SHIMA-R7/Famicom-Expand-USB-Adapter/hardware/schematic/famicom-expand-usb-adapter.kicad_sch

## KiCad design hardware/schematic/famicom-expand-usb-adapter.kicad_sch (2026-08-02)

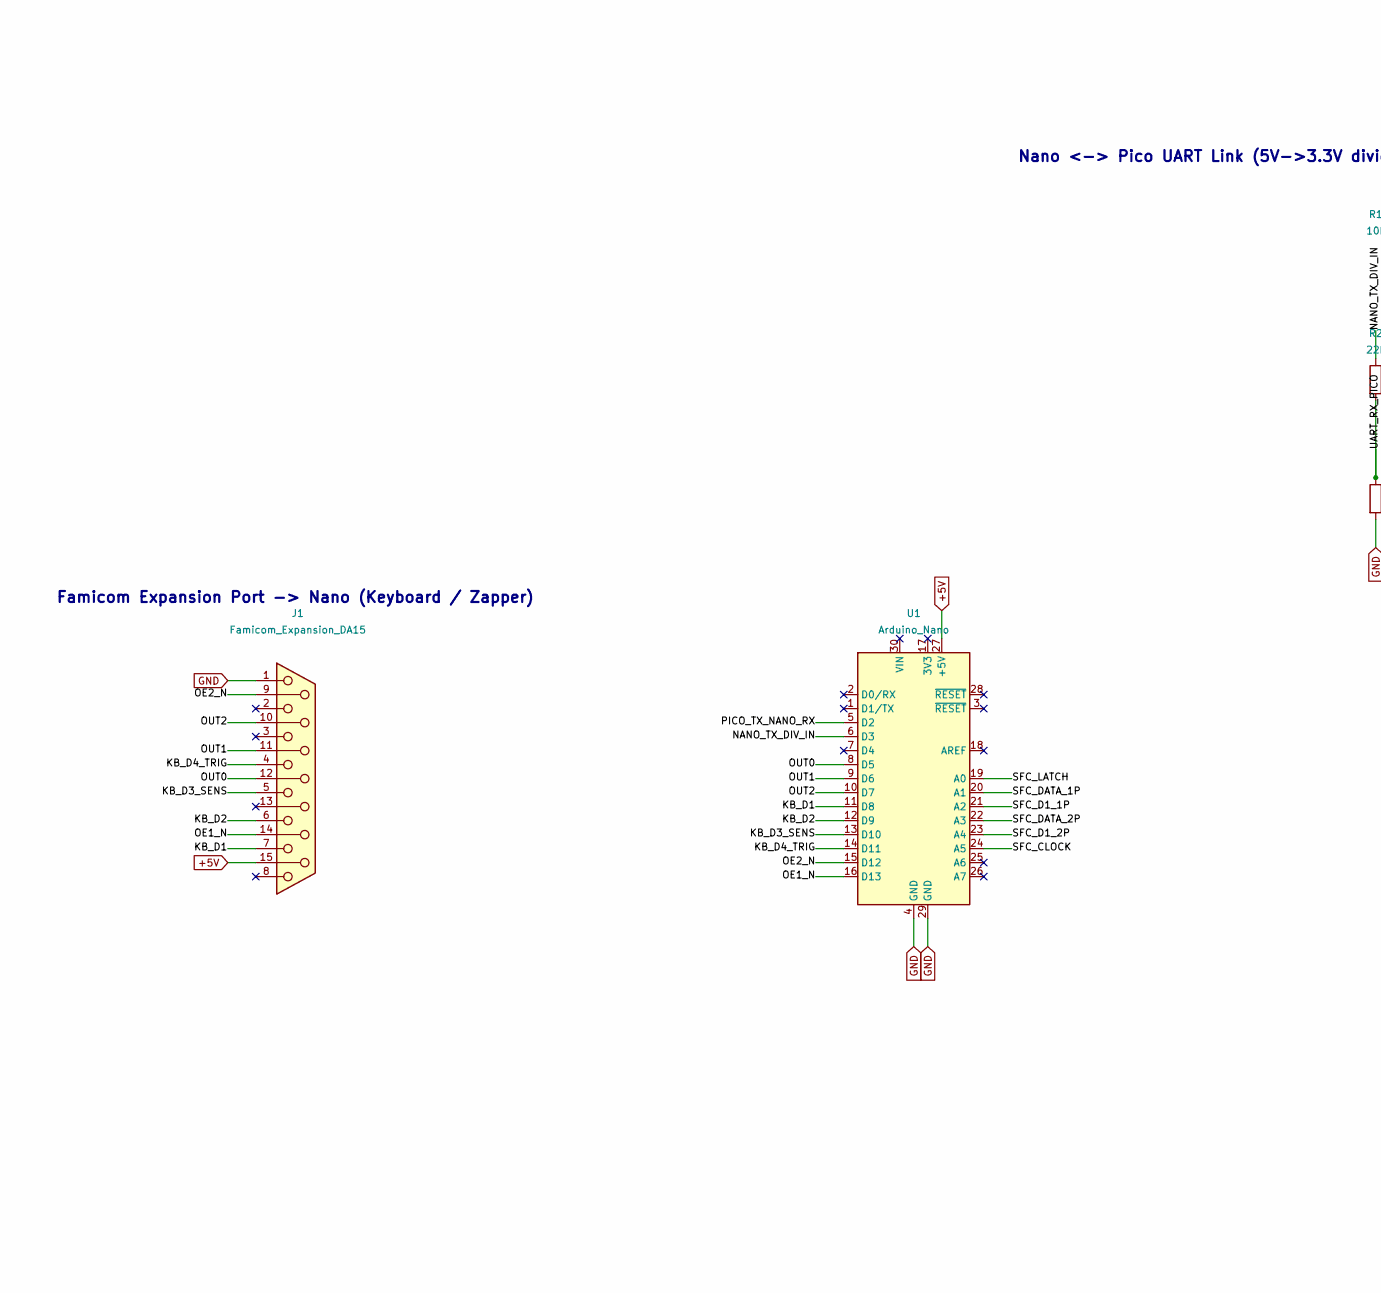
[picture p5: schematic famicom-expand-usb-adapter.kicad_sch, part in row 1, column 1]

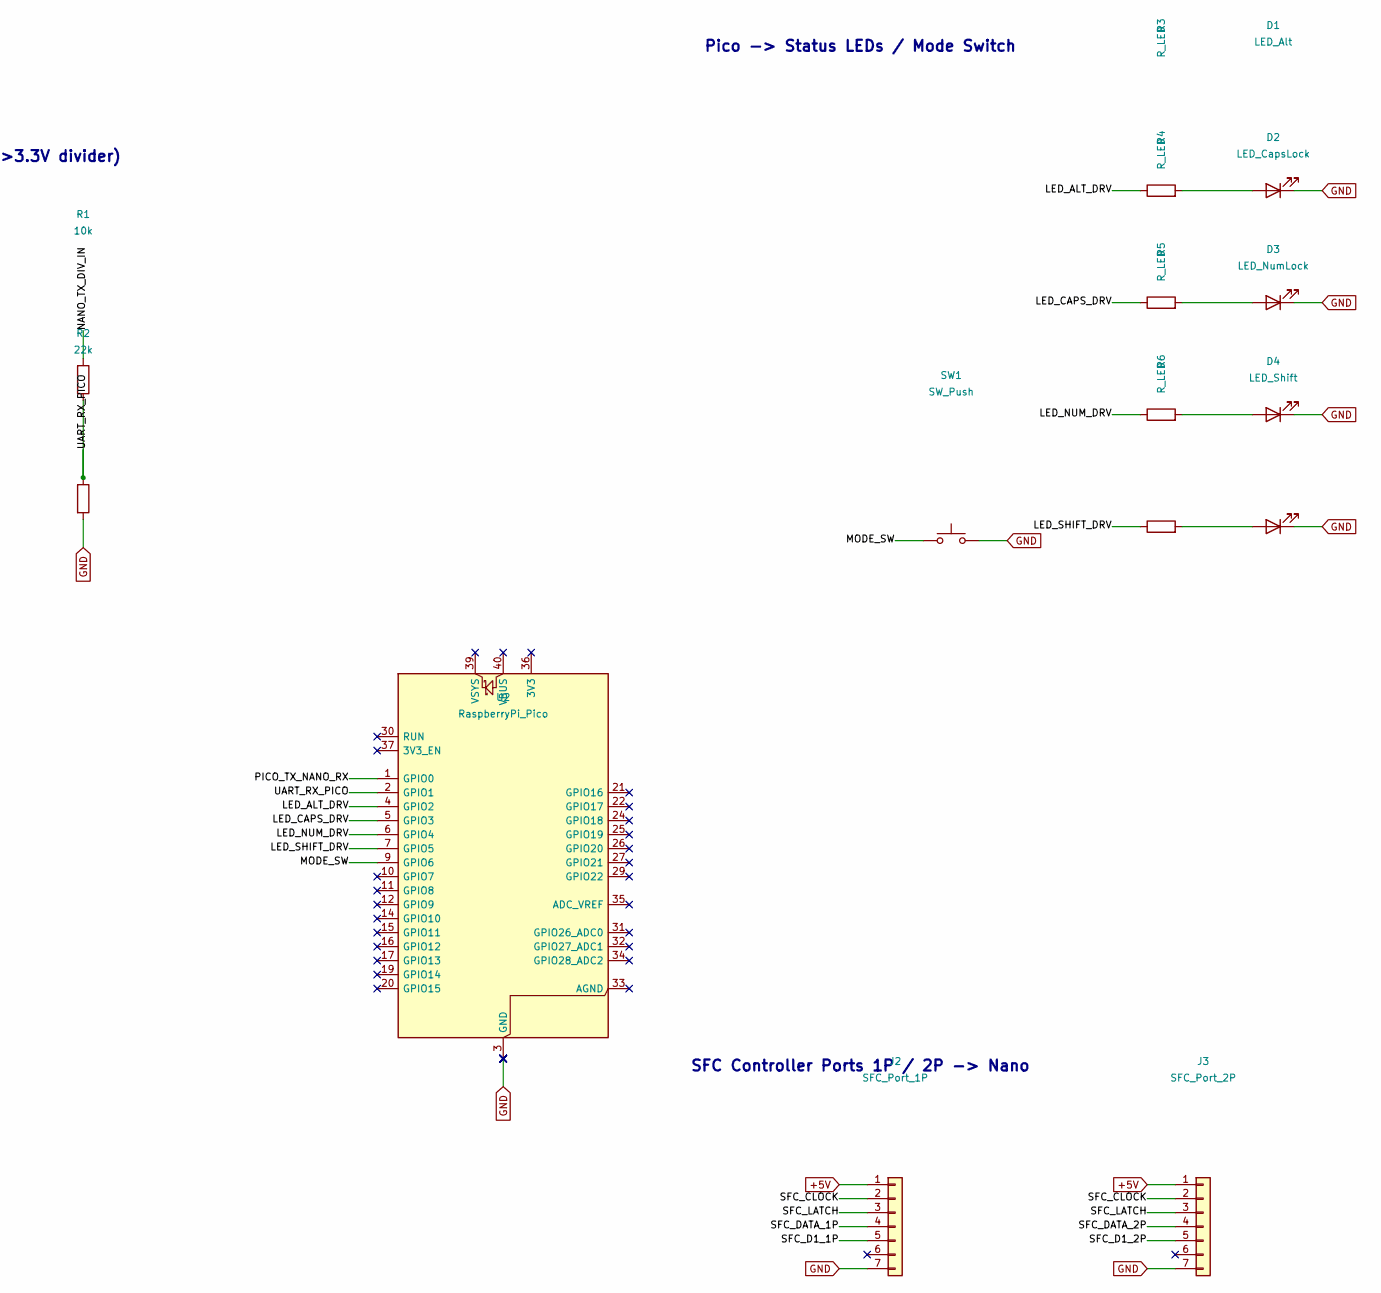
[picture p6: schematic famicom-expand-usb-adapter.kicad_sch, part in row 1, column 2]

Parts:
D1: LED_Alt; LED_D5.0mm
D2: LED_CapsLock; LED_D5.0mm
D3: LED_NumLock; LED_D5.0mm
D4: LED_Shift; LED_D5.0mm
J1: Famicom_Expansion_DA15
J2: SFC_Port_1P; PinHeader_1x07_P2.54mm_Vertical
J3: SFC_Port_2P; PinHeader_1x07_P2.54mm_Vertical
R1: 10k; R_Axial_DIN0207_L6.3mm_D2.5mm_P10.16mm_Horizontal
R2: 22k; R_Axial_DIN0207_L6.3mm_D2.5mm_P10.16mm_Horizontal
R3, R4, R5, R6: R_LED; R_Axial_DIN0207_L6.3mm_D2.5mm_P10.16mm_Horizontal
SW1: SW_Push; SW_PUSH_6mm
U1: Arduino_Nano
U2: RaspberryPi_Pico; RPi_Pico_SMD_TH

Connections:
+5V: J1.15, J2.1, J3.1, U1.27 (+5V)
GND: D1.1 (K), D2.1 (K), D3.1 (K), D4.1 (K), J1.1, J2.7, J3.7, R2.2, SW1.2, U1.4 (GND), U1.29 (GND), U2.3 (GND), U2.8 (GND), U2.13 (GND), U2.18 (GND), U2.23 (GND), U2.28 (GND), U2.38 (GND)
KB_D1: J1.7, U1.11 (D8)
KB_D2: J1.6, U1.12 (D9)
KB_D3_SENS: J1.5, U1.13 (D10)
KB_D4_TRIG: J1.4, U1.14 (D11)
LED_ALT_DRV: R3.1, U2.4 (GPIO2)
LED_CAPS_DRV: R4.1, U2.5 (GPIO3)
LED_NUM_DRV: R5.1, U2.6 (GPIO4)
LED_SHIFT_DRV: R6.1, U2.7 (GPIO5)
MODE_SW: SW1.1, U2.9 (GPIO6)
NANO_TX_DIV_IN: R1.1, U1.6 (D3)
unnamed: D1.2 (A), R3.2
unnamed: D2.2 (A), R4.2
unnamed: D3.2 (A), R5.2
unnamed: D4.2 (A), R6.2
OE1_N: J1.14, U1.16 (D13)
OE2_N: J1.9, U1.15 (D12)
OUT0: J1.12, U1.8 (D5)
OUT1: J1.11 (P111), U1.9 (D6)
OUT2: J1.10, U1.10 (D7)
PICO_TX_NANO_RX: U1.5 (D2), U2.1 (GPIO0)
SFC_CLOCK: J2.2, J3.2, U1.24 (A5)
SFC_D1_1P: J2.5, U1.21 (A2)
SFC_D1_2P: J3.5, U1.23 (A4)
SFC_DATA_1P: J2.4, U1.20 (A1)
SFC_DATA_2P: J3.4, U1.22 (A3)
SFC_LATCH: J2.3, J3.3, U1.19 (A0)
UART_RX_PICO: R1.2, R2.1, U2.2 (GPIO1)

Notes on the sheet:
Famicom Expansion Port -> Nano (Keyboard / Zapper)
Nano <-> Pico UART Link (5V->3.3V divider)
Pico -> Status LEDs / Mode Switch
SFC Controller Ports 1P / 2P -> Nano
